VineetTambe/Integrated_covid19_system/final_integrate/Image/0027.jpg

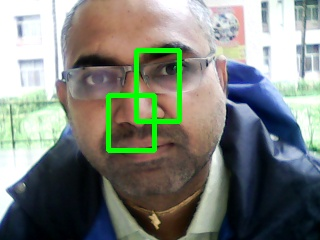
final_integrate/Image/0027.jpg
