VineetTambe/Integrated_covid19_system/final_integrate/Image/84.jpg

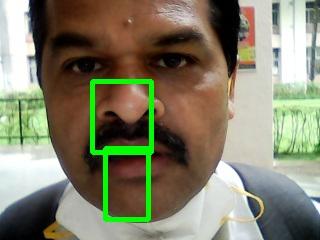
final_integrate/Image/84.jpg
