VineetTambe/Integrated_covid19_system/final_integrate/Image/206.jpg

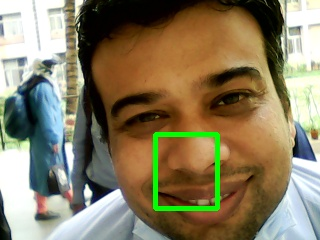
final_integrate/Image/206.jpg
