VineetTambe/Integrated_covid19_system/final_integrate/Image/0248.jpg

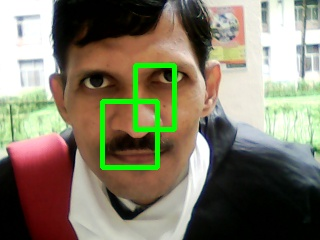
final_integrate/Image/0248.jpg
