VineetTambe/Integrated_covid19_system/final_integrate/Image/273.jpg

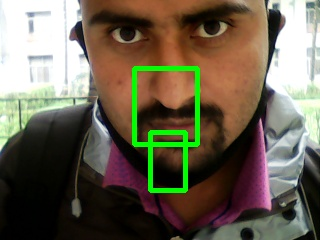
final_integrate/Image/273.jpg
