VineetTambe/Integrated_covid19_system/final_integrate/Image/306.jpg

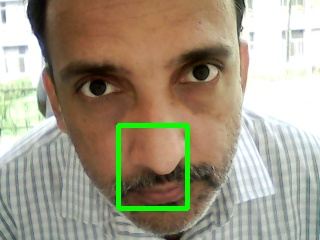
final_integrate/Image/306.jpg
