VineetTambe/Integrated_covid19_system/final_integrate/New/temp_test.py

from smbus2 import SMBus
from mlx90614 import MLX90614

bus = SMBus(1)
sensor = MLX90614(bus, address=0x5A)
while(1):
    #print("ambient")
    #print (sensor.get_ambient())
    #print("temp")
    print (sensor.get_object_1())
bus.close()
